particle-iot/xmastree/docs/android-chrome-192x192.png

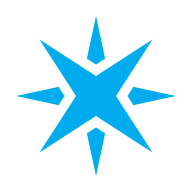
docs/android-chrome-192x192.png
