particle-iot/xmastree/docs/mstile-70x70.png

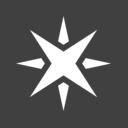
docs/mstile-70x70.png
