particle-iot/xmastree/docs/mstile-144x144.png

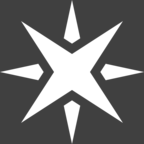
docs/mstile-144x144.png
