particle-iot/xmastree/docs/mstile-150x150.png

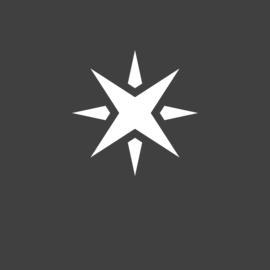
docs/mstile-150x150.png
