particle-iot/xmastree/hardware/images/tree-electron.png

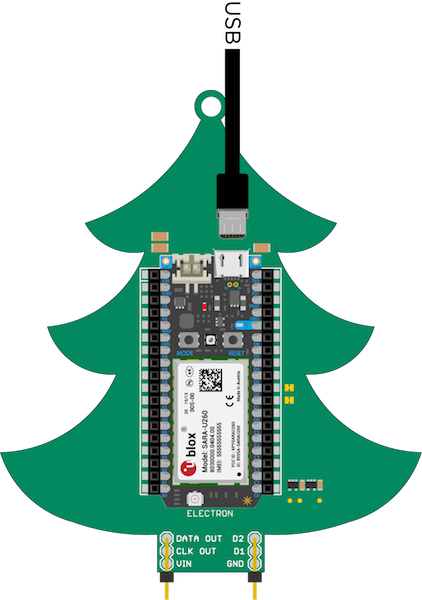
hardware/images/tree-electron.png
