particle-iot/xmastree/hardware/images/step01.jpg

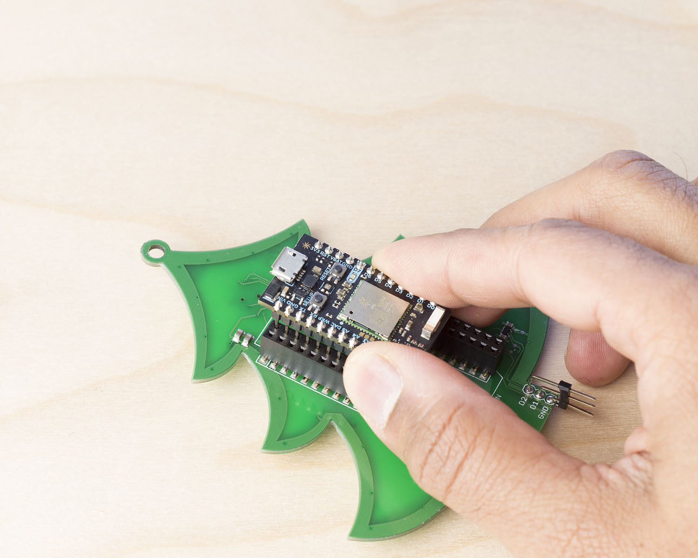
hardware/images/step01.jpg
