particle-iot/xmastree/hardware/images/step02.jpg

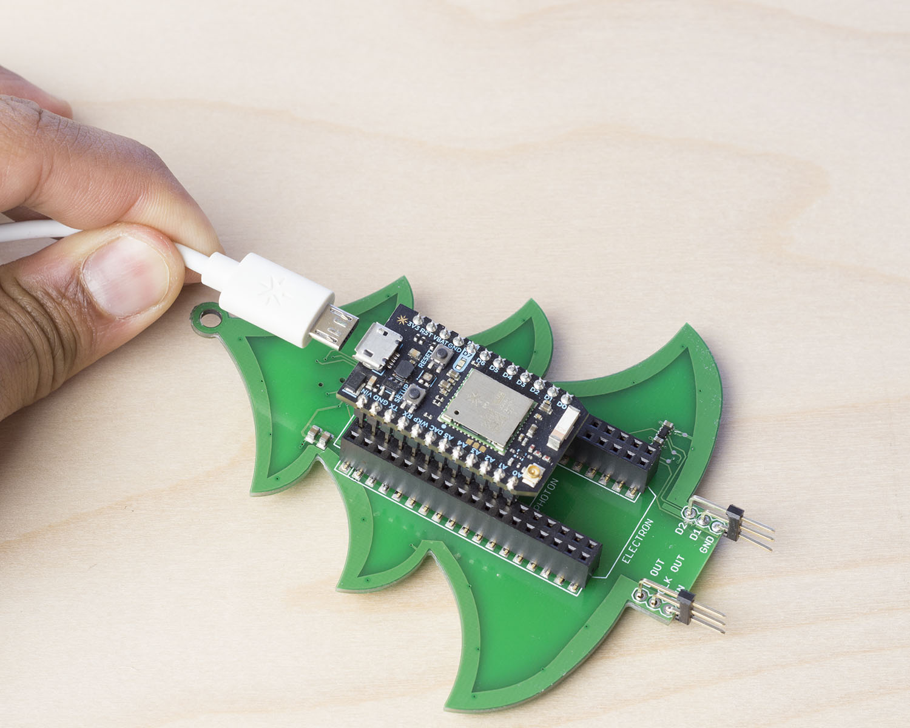
hardware/images/step02.jpg
